F6ITU/K_Munin400/Documentation/hugin_munin.png

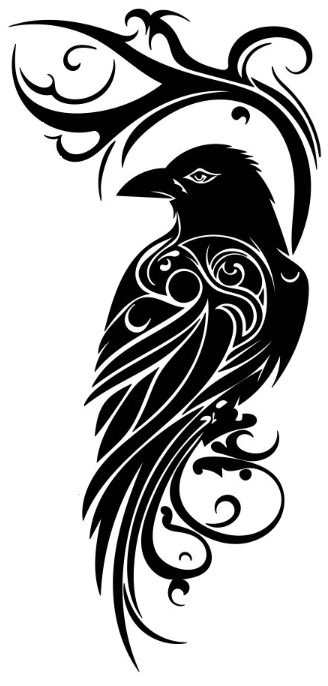
Documentation/hugin_munin.png
